AlexisRichez/timer/04 - stl/Bottom Plate Flip Cover.stl

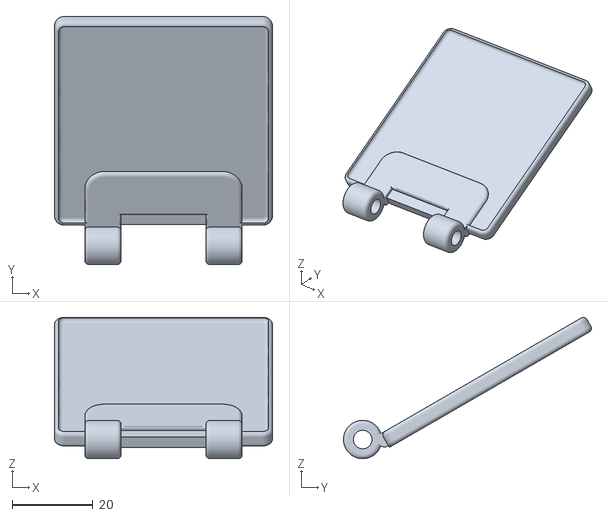
[picture p46: CAD file, 2025-04-23]
04 - stl/Bottom Plate Flip Cover.stl
54.0 x 61.4 x 35.0
