AlexisRichez/timer/04 - stl/Button NAME.stl

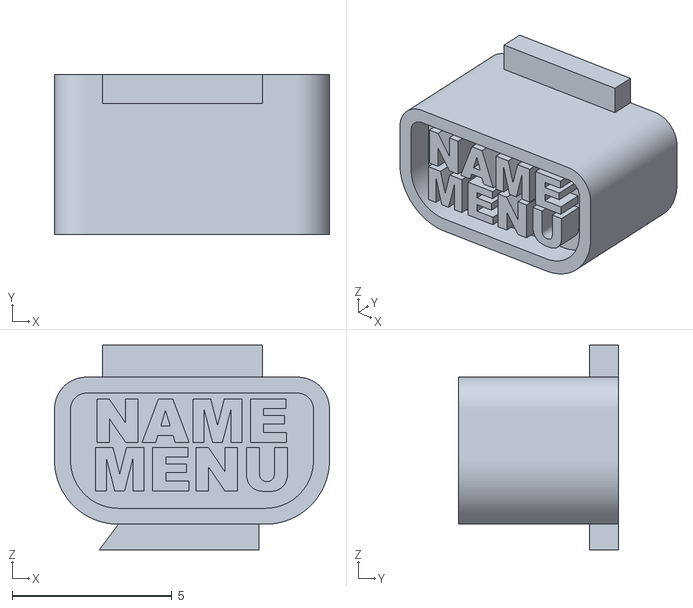
[picture p47: CAD file, 2025-04-23]
04 - stl/Button NAME.stl
8.60 x 5.00 x 6.40
