AlexisRichez/timer/04 - stl/Top Plate Rounded button.stl

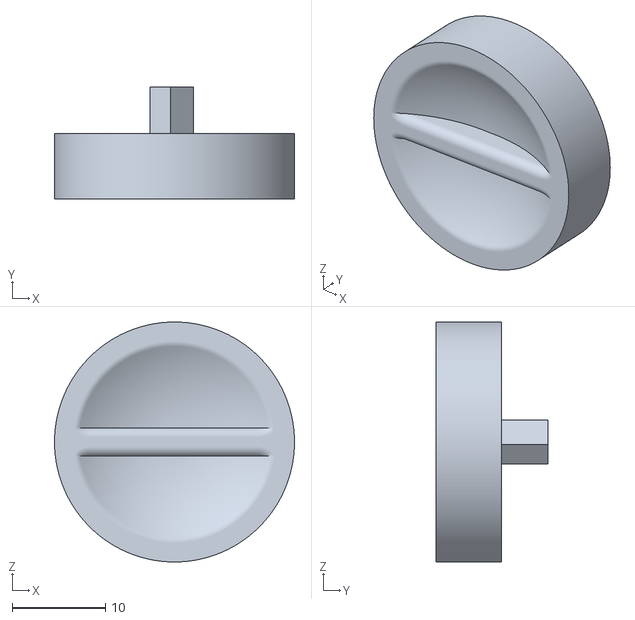
[picture p48: CAD file, 2025-04-23]
04 - stl/Top Plate Rounded button.stl
25.7 x 12.0 x 25.7
