AlexisRichez/timer/04 - stl/Button 4.stl

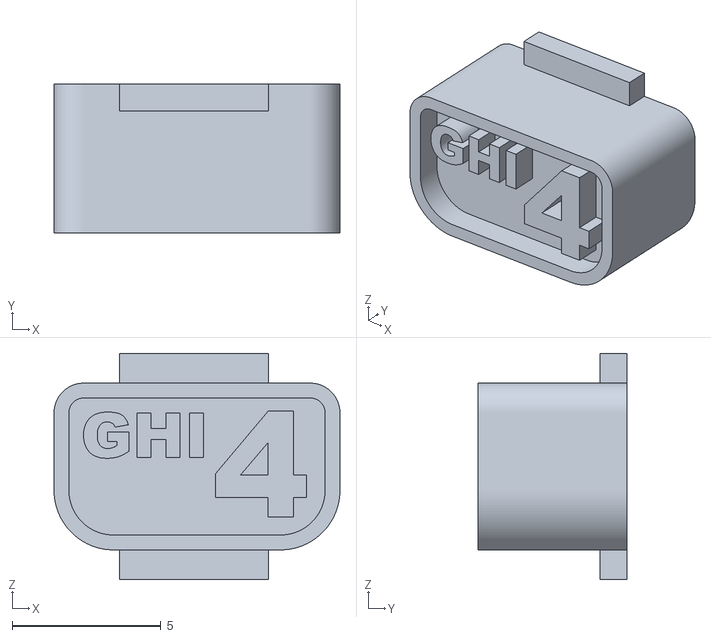
[picture p49: CAD file, 2025-04-23]
04 - stl/Button 4.stl
9.60 x 5.00 x 7.60
