AlexisRichez/timer/04 - stl/Top Plate Laser.stl

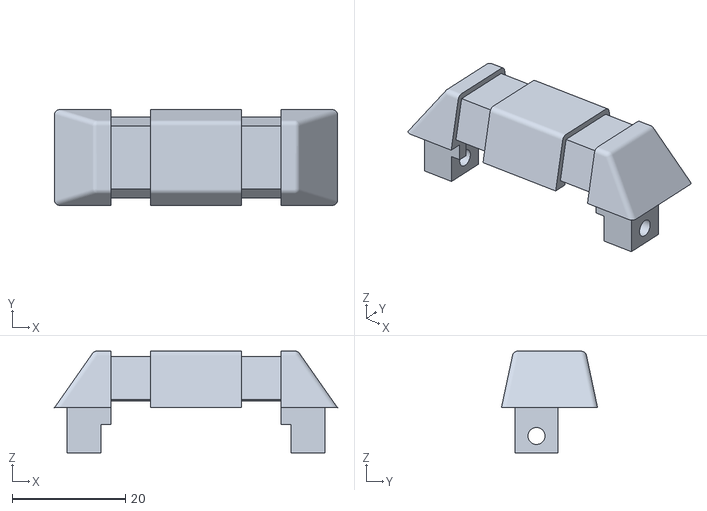
[picture p50: CAD file, 2025-04-23]
04 - stl/Top Plate Laser.stl
50.0 x 17.0 x 18.0
