AlexisRichez/timer/04 - stl/Battery Box Insert.stl

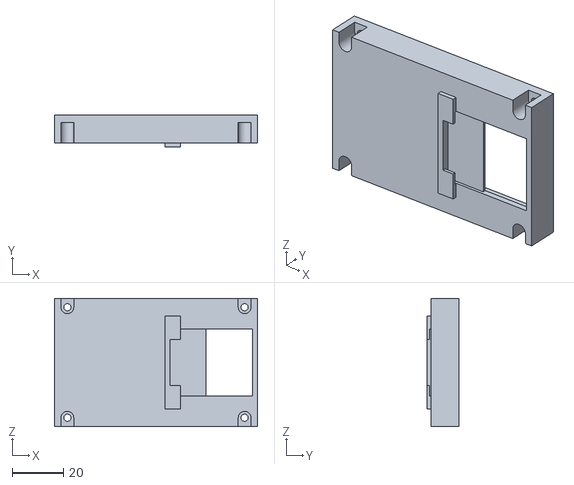
[picture p51: CAD file, 2025-04-23]
04 - stl/Battery Box Insert.stl
79.0 x 12.5 x 50.0
